MattKear/Open-Thrust-Stand/Shaft & Mounts/Shaft-Steel Linear Rail.step

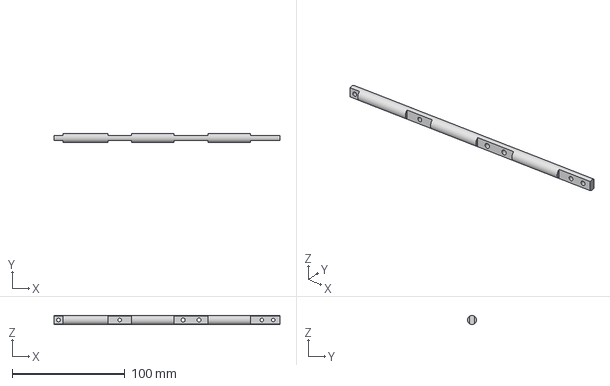
[picture p31: CAD file, 2025-05-01]
Shaft & Mounts/Shaft-Steel Linear Rail.step
200.0 x 7.98 x 7.99 mm
