MattKear/Open-Thrust-Stand/Torque Load Cell Assembly/Torque Cell Interface Bearing Retainer - 3D Print.step

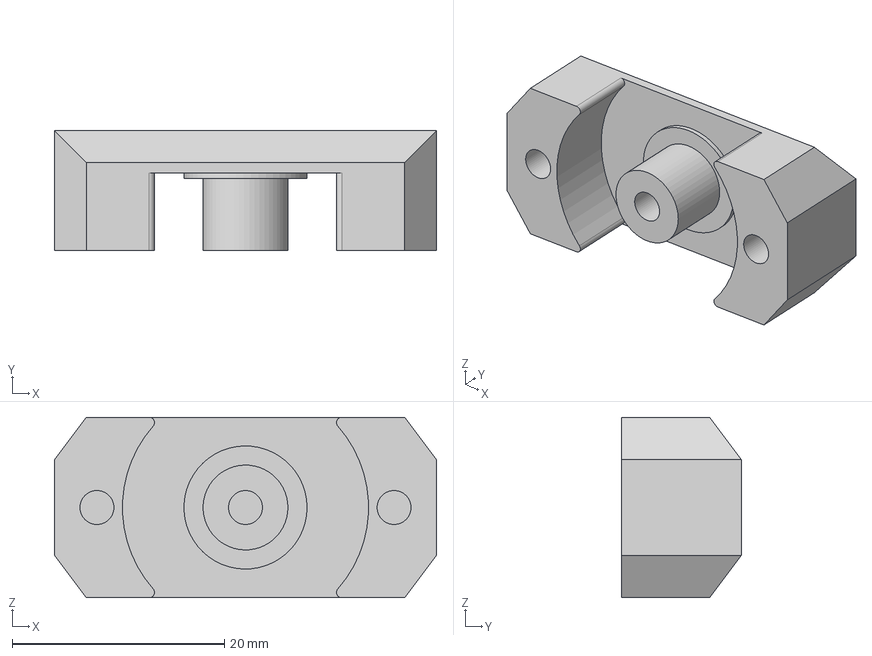
[picture p32: CAD file, 2025-05-01]
Torque Load Cell Assembly/Torque Cell Interface Bearing Retainer - 3D Print.step
36.0 x 11.3 x 17.0 mm
