MattKear/Open-Thrust-Stand/Torque Load Cell Assembly/Torque Cell Interface Case - 3D Print.step

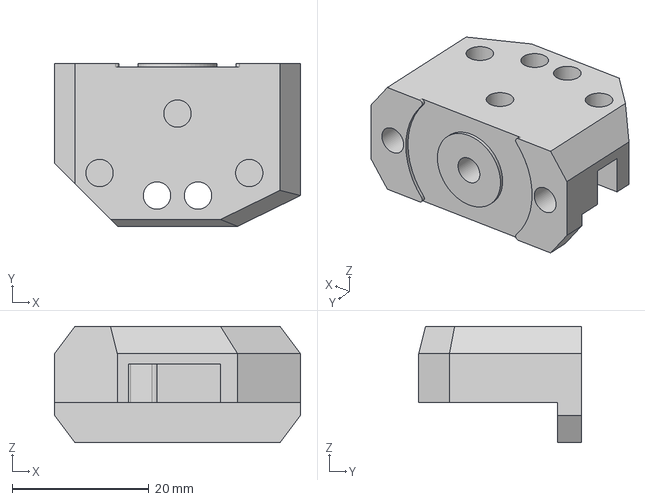
[picture p33: CAD file, 2025-05-01]
Torque Load Cell Assembly/Torque Cell Interface Case - 3D Print.step
36.0 x 23.8 x 17.0 mm
