MattKear/Open-Thrust-Stand/Torque Load Cell Assembly/TorqueShaftClampRight-3DPrint.step

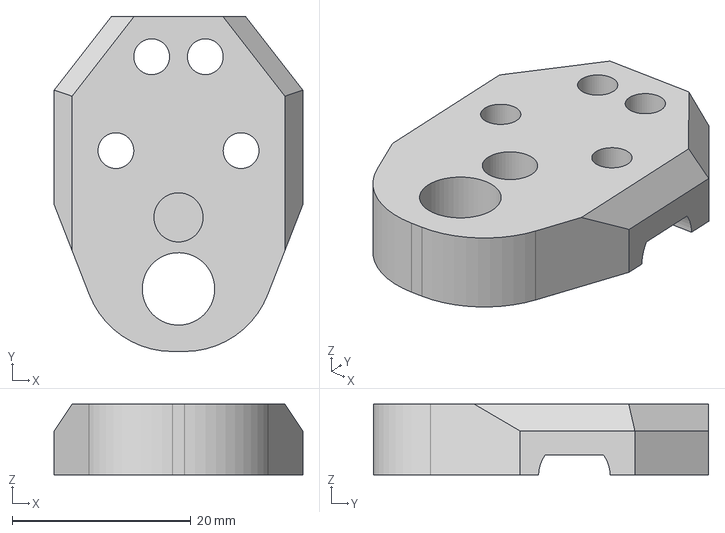
[picture p34: CAD file, 2025-05-01]
Torque Load Cell Assembly/TorqueShaftClampRight-3DPrint.step
27.8 x 37.5 x 7.90 mm
