MattKear/Open-Thrust-Stand/Torque Load Cell Assembly/Torque Load Cell.step

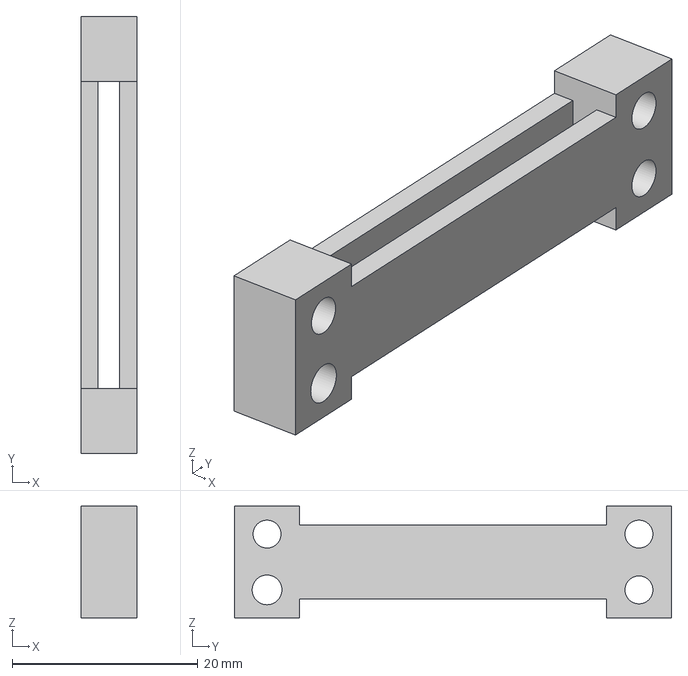
[picture p35: CAD file, 2025-05-01]
Torque Load Cell Assembly/Torque Load Cell.step
6.00 x 47.0 x 12.0 mm
